MonitorAmbientLight/mal-master/pictures/30.jpeg

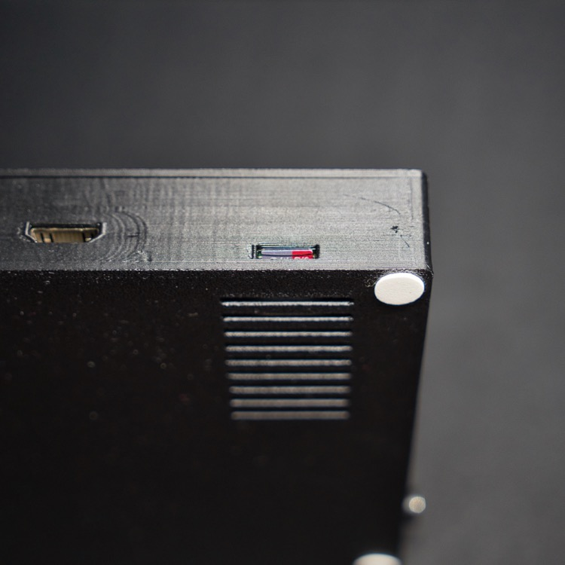
pictures/30.jpeg
